rk-kaps/RKS-KEYBOARD/PCB/PCB.kicad_sch

## KiCad design PCB/PCB.kicad_sch (2026-03-29)

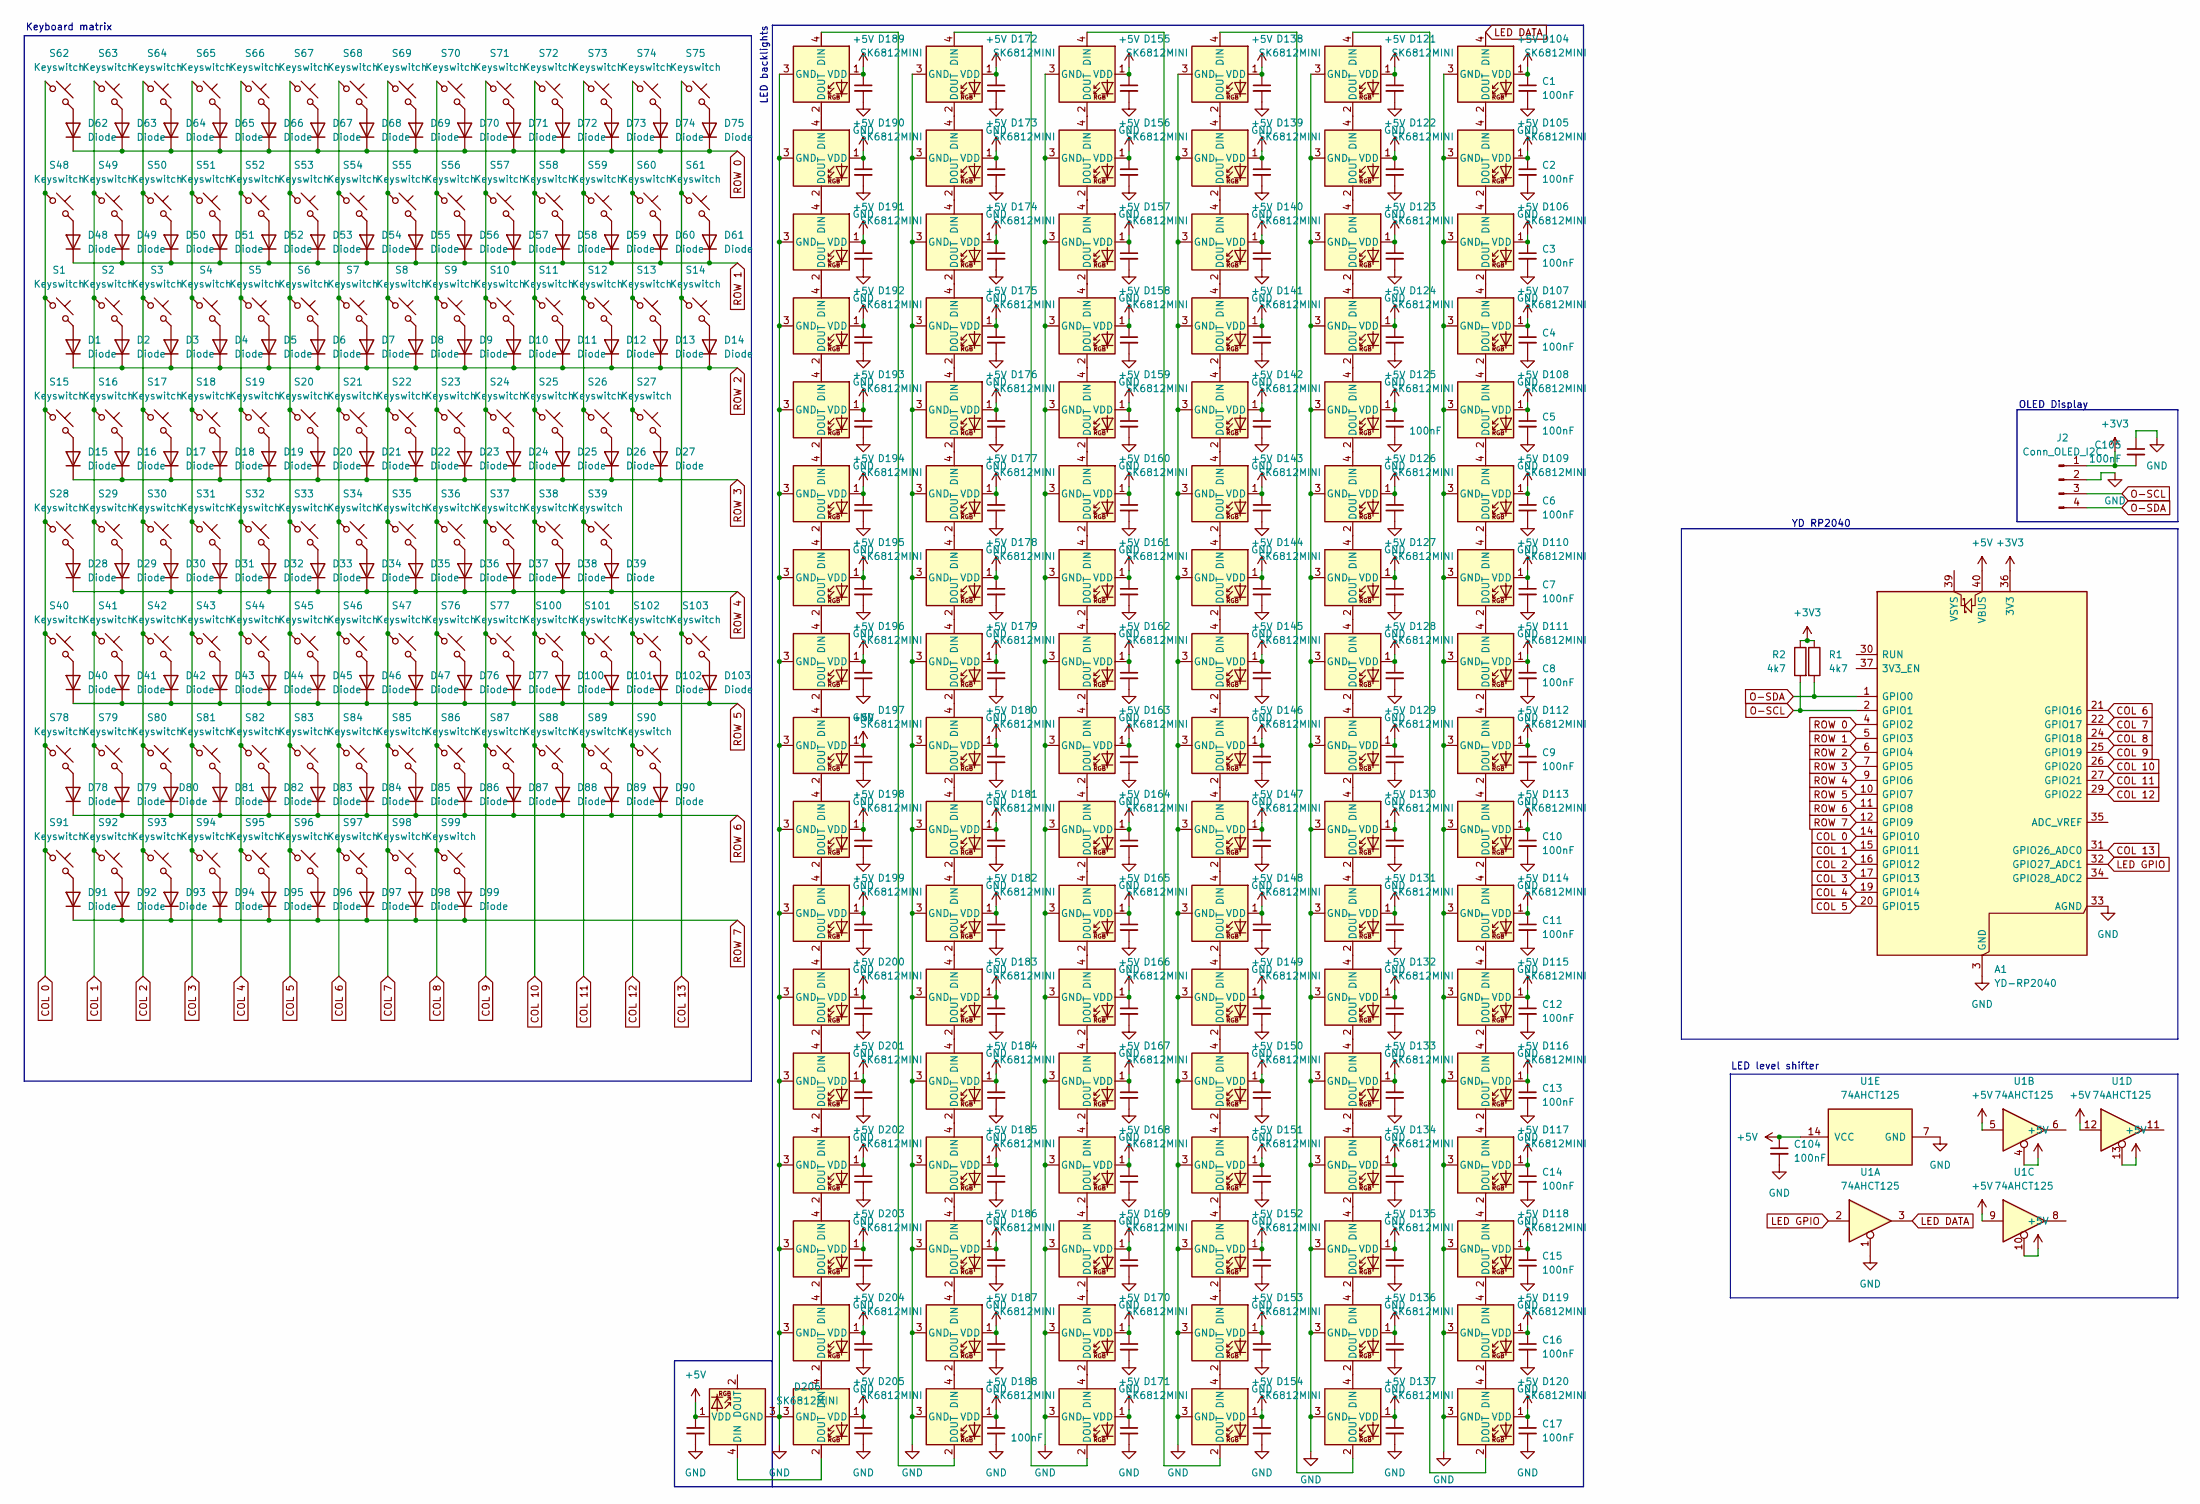
[picture p13: schematic PCB.kicad_sch]

Parts:
A1: YD-RP2040; RaspberryPi_Pico_SMD_HandSolder
C1, C2, C3, C4, C5, C6, C7, C8, C9, C10, C11, C12, C13, C14, C15, C16, C17, C18, C19, C20, C21, C22, C23, C24, C25, C26, C27, C28, C29, C30, C31, C32, C33, C34, C35, C36, C37, C38, C39, C40, C41, C42, C43, C44, C45, C46, C47, C48, C49, C50, C51, C52, C53, C54, C55, C56, C57, C58, C59, C60, C61, C62, C63, C64, C65, C66, C67, C68, C69, C70, C71, C72, C73, C74, C75, C76, C77, C78, C79, C80, C81, C82, C83, C84, C85, C86, C87, C88, C89, C90, C91, C92, C93, C94, C95, C96, C97, C98, C99, C100, C101, C102, C103, C104, C105: 100nF; C_0805_2012Metric_Pad1.18x1.45mm_HandSolder
D1, D2, D3, D4, D5, D6, D7, D8, D9, D10, D11, D12, D13, D14, D15, D16, D17, D18, D19, D20, D21, D22, D23, D24, D25, D26, D27, D28, D29, D30, D31, D32, D33, D34, D35, D36, D37, D38, D39, D40, D41, D42, D43, D44, D45, D46, D47, D48, D49, D50, D51, D52, D53, D54, D55, D56, D57, D58, D59, D60, D61, D62, D63, D64, D65, D66, D67, D68, D69, D70, D71, D72, D73, D74, D75, D76, D77, D78, D79, D80, D81, D82, D83, D84, D85, D86, D87, D88, D89, D90, D91, D92, D93, D94, D95, D96, D97, D98, D99, D100, D101, D102, D103: Diode; Diode_SOD-123
D104, D105, D106, D107, D108, D109, D110, D111, D112, D113, D114, D115, D116, D117, D118, D119, D120, D121, D122, D123, D124, D125, D126, D127, D128, D129, D130, D131, D132, D133, D134, D135, D136, D137, D138, D139, D140, D141, D142, D143, D144, D145, D146, D147, D148, D149, D150, D151, D152, D153, D154, D155, D156, D157, D158, D159, D160, D161, D162, D163, D164, D165, D166, D167, D168, D169, D170, D171, D172, D173, D174, D175, D176, D177, D178, D179, D180, D181, D182, D183, D184, D185, D186, D187, D188, D189, D190, D191, D192, D193, D194, D195, D196, D197, D198, D199, D200, D201, D202, D203, D204, D205, D206: SK6812MINI; LED_SK6812MINI
J2: Conn_OLED_I2C; PinHeader_1x04_P2.54mm_Vertical
R1, R2: 4k7; R_0805_2012Metric_Pad1.20x1.40mm_HandSolder
S1, S14: Keyswitch; Hotswap_MX_1.50u
S2, S3, S4, S5, S6, S7, S8, S9, S10, S11, S12, S13, S16, S17, S18, S19, S20, S21, S22, S23, S24, S25, S26, S29, S30, S31, S32, S33, S34, S35, S36, S37, S38, S44, S45, S46, S47, S48, S49, S50, S51, S52, S53, S54, S55, S56, S57, S58, S59, S60, S62, S63, S64, S65, S66, S67, S68, S69, S70, S71, S72, S73, S74, S75, S76, S77, S78, S79, S80, S81, S82, S83, S84, S85, S86, S87, S88, S89, S90, S91, S92, S95, S96, S97, S98, S99, S100, S101, S102, S103: Keyswitch; Hotswap_MX_1.00u
S15, S39: Keyswitch; Hotswap_MX_1.75u
S27, S28: Keyswitch; Hotswap_MX_2.25u
S40, S41, S42: Keyswitch; Hotswap_MX_1.25u
S43: Keyswitch; Hotswap_MX_6.25u
S61: Keyswitch; Hotswap_MX_2.00u
S93, S94: Keyswitch; Hotswap_MX_2.00u_90deg
U1: 74AHCT125; SOIC-14_3.9x8.7mm_P1.27mm

Connections:
+3V3: A1.36 (3V3), C105.2, J2.1, R1.1, R2.1
+5V: A1.40 (VBUS), C1.1, C2.1, C3.1, C4.1, C5.1, C6.1, C7.1, C8.1, C9.1, C10.1, C11.1, C12.1, C13.1, C14.1, C15.1, C16.1, C17.1, C18.1, C19.1, C20.1, C21.1, C22.1, C23.1, C24.1, C25.1, C26.1, C27.1, C28.1, C29.1, C30.1, C31.1, C32.1, C33.1, C34.1, C35.1, C36.1, C37.1, C38.1, C39.1, C40.1, C41.1, C42.1, C43.1, C44.1, C45.1, C46.1, C47.1, C48.1, C49.1, C50.1, C51.1, C52.1, C53.1, C54.1, C55.1, C56.1, C57.1, C58.1, C59.1, C60.1, C61.1, C62.1, C63.1, C64.1, C65.1, C66.1, C67.1, C68.1, C69.1, C70.1, C71.1, C72.1, C73.1, C74.1, C75.1, C76.1, C77.1, C78.1, C79.1, C80.1, C81.1, C82.1, C83.1, C84.1, C85.1, C86.1, C87.1, C88.1, C89.1, C90.1, C91.1, C92.1, C93.1, C94.1, C95.1, C96.1, C97.1, C98.1, C99.1, C100.1, C101.1, C102.1, C103.1, C104.1, D104.1 (VDD), D105.1 (VDD), D106.1 (VDD), D107.1 (VDD), D108.1 (VDD), D109.1 (VDD), D110.1 (VDD), D111.1 (VDD), D112.1 (VDD), D113.1 (VDD), D114.1 (VDD), D115.1 (VDD), D116.1 (VDD), D117.1 (VDD), D118.1 (VDD), D119.1 (VDD), D120.1 (VDD), D121.1 (VDD), D122.1 (VDD), D123.1 (VDD), D124.1 (VDD), D125.1 (VDD), D126.1 (VDD), D127.1 (VDD), D128.1 (VDD), D129.1 (VDD), D130.1 (VDD), D131.1 (VDD), D132.1 (VDD), D133.1 (VDD), D134.1 (VDD), D135.1 (VDD), D136.1 (VDD), D137.1 (VDD), D138.1 (VDD), D139.1 (VDD), D140.1 (VDD), D141.1 (VDD), D142.1 (VDD), D143.1 (VDD), D144.1 (VDD), D145.1 (VDD), D146.1 (VDD), D147.1 (VDD), D148.1 (VDD), D149.1 (VDD), D150.1 (VDD), D151.1 (VDD), D152.1 (VDD), D153.1 (VDD), D154.1 (VDD), D155.1 (VDD), D156.1 (VDD), D157.1 (VDD), D158.1 (VDD), D159.1 (VDD), D160.1 (VDD), D161.1 (VDD), D162.1 (VDD), D163.1 (VDD), D164.1 (VDD), D165.1 (VDD), D166.1 (VDD), D167.1 (VDD), D168.1 (VDD), D169.1 (VDD), D170.1 (VDD), D171.1 (VDD), D172.1 (VDD), D173.1 (VDD), D174.1 (VDD), D175.1 (VDD), D176.1 (VDD), D177.1 (VDD), D178.1 (VDD), D179.1 (VDD), D180.1 (VDD), D181.1 (VDD), D182.1 (VDD), D183.1 (VDD), D184.1 (VDD), D185.1 (VDD), D186.1 (VDD), D187.1 (VDD), D188.1 (VDD), D189.1 (VDD), D190.1 (VDD), D191.1 (VDD), D192.1 (VDD), D193.1 (VDD), D194.1 (VDD), D195.1 (VDD), D196.1 (VDD), D197.1 (VDD), D198.1 (VDD), D199.1 (VDD), D200.1 (VDD), D201.1 (VDD), D202.1 (VDD), D203.1 (VDD), D204.1 (VDD), D205.1 (VDD), D206.1 (VDD), U1.4, U1.5, U1.9, U1.10, U1.12, U1.13, U1.14 (VCC)
COL 0: A1.14 (GPIO10), S1.1, S15.1, S28.1, S40.1, S48.1, S62.1, S78.1, S91.1
COL 1: A1.15 (GPIO11), S2.1, S16.1, S29.1, S41.1, S49.1, S63.1, S79.1, S92.1
COL 2: A1.16 (GPIO12), S3.1, S17.1, S30.1, S42.1, S50.1, S64.1, S80.1, S93.1
COL 3: A1.17 (GPIO13), S4.1, S18.1, S31.1, S43.1, S51.1, S65.1, S81.1, S94.1
COL 4: A1.19 (GPIO14), S5.1, S19.1, S32.1, S44.1, S52.1, S66.1, S82.1, S95.1
COL 5: A1.20 (GPIO15), S6.1, S20.1, S33.1, S45.1, S53.1, S67.1, S83.1, S96.1
COL 6: A1.21 (GPIO16), S7.1, S21.1, S34.1, S46.1, S54.1, S68.1, S84.1, S97.1
COL 7: A1.22 (GPIO17), S8.1, S22.1, S35.1, S47.1, S55.1, S69.1, S85.1, S98.1
COL 8: A1.24 (GPIO18), S9.1, S23.1, S36.1, S56.1, S70.1, S76.1, S86.1, S99.1
COL 9: A1.25 (GPIO19), S10.1, S24.1, S37.1, S57.1, S71.1, S77.1, S87.1
COL 10: A1.26 (GPIO20), S11.1, S25.1, S38.1, S58.1, S72.1, S88.1, S100.1
COL 11: A1.27 (GPIO21), S12.1, S26.1, S39.1, S59.1, S73.1, S89.1, S101.1
COL 12: A1.29 (GPIO22), S13.1, S27.1, S60.1, S74.1, S90.1, S102.1
COL 13: A1.31 (GPIO26_ADC0), S14.1, S61.1, S75.1, S103.1
GND: A1.3 (GND), A1.8 (GND), A1.13 (GND), A1.18 (GND), A1.23 (GND), A1.28 (GND), A1.33 (AGND), A1.38 (GND), C1.2, C2.2, C3.2, C4.2, C5.2, C6.2, C7.2, C8.2, C9.2, C10.2, C11.2, C12.2, C13.2, C14.2, C15.2, C16.2, C17.2, C18.2, C19.2, C20.2, C21.2, C22.2, C23.2, C24.2, C25.2, C26.2, C27.2, C28.2, C29.2, C30.2, C31.2, C32.2, C33.2, C34.2, C35.2, C36.2, C37.2, C38.2, C39.2, C40.2, C41.2, C42.2, C43.2, C44.2, C45.2, C46.2, C47.2, C48.2, C49.2, C50.2, C51.2, C52.2, C53.2, C54.2, C55.2, C56.2, C57.2, C58.2, C59.2, C60.2, C61.2, C62.2, C63.2, C64.2, C65.2, C66.2, C67.2, C68.2, C69.2, C70.2, C71.2, C72.2, C73.2, C74.2, C75.2, C76.2, C77.2, C78.2, C79.2, C80.2, C81.2, C82.2, C83.2, C84.2, C85.2, C86.2, C87.2, C88.2, C89.2, C90.2, C91.2, C92.2, C93.2, C94.2, C95.2, C96.2, C97.2, C98.2, C99.2, C100.2, C101.2, C102.2, C103.2, C104.2, C105.1, D104.3 (GND), D105.3 (GND), D106.3 (GND), D107.3 (GND), D108.3 (GND), D109.3 (GND), D110.3 (GND), D111.3 (GND), D112.3 (GND), D113.3 (GND), D114.3 (GND), D115.3 (GND), D116.3 (GND), D117.3 (GND), D118.3 (GND), D119.3 (GND), D120.3 (GND), D121.3 (GND), D122.3 (GND), D123.3 (GND), D124.3 (GND), D125.3 (GND), D126.3 (GND), D127.3 (GND), D128.3 (GND), D129.3 (GND), D130.3 (GND), D131.3 (GND), D132.3 (GND), D133.3 (GND), D134.3 (GND), D135.3 (GND), D136.3 (GND), D137.3 (GND), D138.3 (GND), D139.3 (GND), D140.3 (GND), D141.3 (GND), D142.3 (GND), D143.3 (GND), D144.3 (GND), D145.3 (GND), D146.3 (GND), D147.3 (GND), D148.3 (GND), D149.3 (GND), D150.3 (GND), D151.3 (GND), D152.3 (GND), D153.3 (GND), D154.3 (GND), D155.3 (GND), D156.3 (GND), D157.3 (GND), D158.3 (GND), D159.3 (GND), D160.3 (GND), D161.3 (GND), D162.3 (GND), D163.3 (GND), D164.3 (GND), D165.3 (GND), D166.3 (GND), D167.3 (GND), D168.3 (GND), D169.3 (GND), D170.3 (GND), D171.3 (GND), D172.3 (GND), D173.3 (GND), D174.3 (GND), D175.3 (GND), D176.3 (GND), D177.3 (GND), D178.3 (GND), D179.3 (GND), D180.3 (GND), D181.3 (GND), D182.3 (GND), D183.3 (GND), D184.3 (GND), D185.3 (GND), D186.3 (GND), D187.3 (GND), D188.3 (GND), D189.3 (GND), D190.3 (GND), D191.3 (GND), D192.3 (GND), D193.3 (GND), D194.3 (GND), D195.3 (GND), D196.3 (GND), D197.3 (GND), D198.3 (GND), D199.3 (GND), D200.3 (GND), D201.3 (GND), D202.3 (GND), D203.3 (GND), D204.3 (GND), D205.3 (GND), D206.3 (GND), J2.2, U1.1, U1.7 (GND)
LED DATA: D104.4 (DIN), U1.3
LED GPIO: A1.32 (GPIO27_ADC1), U1.2
unnamed: D1.2 (A), S1.2
unnamed: D2.2 (A), S2.2
unnamed: D3.2 (A), S3.2
unnamed: D4.2 (A), S4.2
unnamed: D5.2 (A), S5.2
unnamed: D6.2 (A), S6.2
unnamed: D7.2 (A), S7.2
unnamed: D8.2 (A), S8.2
unnamed: D9.2 (A), S9.2
unnamed: D10.2 (A), S10.2
unnamed: D11.2 (A), S11.2
unnamed: D12.2 (A), S12.2
unnamed: D13.2 (A), S13.2
unnamed: D14.2 (A), S14.2
unnamed: D15.2 (A), S15.2
unnamed: D16.2 (A), S16.2
unnamed: D17.2 (A), S17.2
unnamed: D18.2 (A), S18.2
unnamed: D19.2 (A), S19.2
unnamed: D20.2 (A), S20.2
unnamed: D21.2 (A), S21.2
unnamed: D22.2 (A), S22.2
unnamed: D23.2 (A), S23.2
unnamed: D24.2 (A), S24.2
unnamed: D25.2 (A), S25.2
unnamed: D26.2 (A), S26.2
unnamed: D27.2 (A), S27.2
unnamed: D28.2 (A), S28.2
unnamed: D29.2 (A), S29.2
unnamed: D30.2 (A), S30.2
unnamed: D31.2 (A), S31.2
unnamed: D32.2 (A), S32.2
unnamed: D33.2 (A), S33.2
unnamed: D34.2 (A), S34.2
unnamed: D35.2 (A), S35.2
unnamed: D36.2 (A), S36.2
unnamed: D37.2 (A), S37.2
unnamed: D38.2 (A), S38.2
unnamed: D39.2 (A), S39.2
unnamed: D40.2 (A), S40.2
unnamed: D41.2 (A), S41.2
unnamed: D42.2 (A), S42.2
unnamed: D43.2 (A), S43.2
unnamed: D44.2 (A), S44.2
unnamed: D45.2 (A), S45.2
unnamed: D46.2 (A), S46.2
unnamed: D47.2 (A), S47.2
unnamed: D48.2 (A), S48.2
unnamed: D49.2 (A), S49.2
unnamed: D50.2 (A), S50.2
unnamed: D51.2 (A), S51.2
unnamed: D52.2 (A), S52.2
unnamed: D53.2 (A), S53.2
unnamed: D54.2 (A), S54.2
unnamed: D55.2 (A), S55.2
unnamed: D56.2 (A), S56.2
unnamed: D57.2 (A), S57.2
unnamed: D58.2 (A), S58.2
unnamed: D59.2 (A), S59.2
unnamed: D60.2 (A), S60.2
unnamed: D61.2 (A), S61.2
unnamed: D62.2 (A), S62.2
unnamed: D63.2 (A), S63.2
unnamed: D64.2 (A), S64.2
unnamed: D65.2 (A), S65.2
unnamed: D66.2 (A), S66.2
unnamed: D67.2 (A), S67.2
unnamed: D68.2 (A), S68.2
unnamed: D69.2 (A), S69.2
unnamed: D70.2 (A), S70.2
unnamed: D71.2 (A), S71.2
unnamed: D72.2 (A), S72.2
unnamed: D73.2 (A), S73.2
unnamed: D74.2 (A), S74.2
unnamed: D75.2 (A), S75.2
unnamed: D76.2 (A), S76.2
unnamed: D77.2 (A), S77.2
unnamed: D78.2 (A), S78.2
unnamed: D79.2 (A), S79.2
unnamed: D80.2 (A), S80.2
unnamed: D81.2 (A), S81.2
unnamed: D82.2 (A), S82.2
unnamed: D83.2 (A), S83.2
unnamed: D84.2 (A), S84.2
unnamed: D85.2 (A), S85.2
unnamed: D86.2 (A), S86.2
unnamed: D87.2 (A), S87.2
unnamed: D88.2 (A), S88.2
unnamed: D89.2 (A), S89.2
unnamed: D90.2 (A), S90.2
unnamed: D91.2 (A), S91.2
unnamed: D92.2 (A), S92.2
unnamed: D93.2 (A), S93.2
unnamed: D94.2 (A), S94.2
unnamed: D95.2 (A), S95.2
unnamed: D96.2 (A), S96.2
unnamed: D97.2 (A), S97.2
unnamed: D98.2 (A), S98.2
unnamed: D99.2 (A), S99.2
unnamed: D100.2 (A), S100.2
unnamed: D101.2 (A), S101.2
unnamed: D102.2 (A), S102.2
unnamed: D103.2 (A), S103.2
unnamed: D104.2 (DOUT), D105.4 (DIN)
unnamed: D105.2 (DOUT), D106.4 (DIN)
unnamed: D106.2 (DOUT), D107.4 (DIN)
unnamed: D107.2 (DOUT), D108.4 (DIN)
unnamed: D108.2 (DOUT), D109.4 (DIN)
unnamed: D109.2 (DOUT), D110.4 (DIN)
unnamed: D110.2 (DOUT), D111.4 (DIN)
unnamed: D111.2 (DOUT), D112.4 (DIN)
unnamed: D112.2 (DOUT), D113.4 (DIN)
unnamed: D113.2 (DOUT), D114.4 (DIN)
unnamed: D114.2 (DOUT), D115.4 (DIN)
unnamed: D115.2 (DOUT), D116.4 (DIN)
unnamed: D116.2 (DOUT), D117.4 (DIN)
unnamed: D117.2 (DOUT), D118.4 (DIN)
unnamed: D118.2 (DOUT), D119.4 (DIN)
unnamed: D119.2 (DOUT), D120.4 (DIN)
unnamed: D120.2 (DOUT), D121.4 (DIN)
unnamed: D121.2 (DOUT), D122.4 (DIN)
unnamed: D122.2 (DOUT), D123.4 (DIN)
unnamed: D123.2 (DOUT), D124.4 (DIN)
unnamed: D124.2 (DOUT), D125.4 (DIN)
unnamed: D125.2 (DOUT), D126.4 (DIN)
unnamed: D126.2 (DOUT), D127.4 (DIN)
unnamed: D127.2 (DOUT), D128.4 (DIN)
unnamed: D128.2 (DOUT), D129.4 (DIN)
unnamed: D129.2 (DOUT), D130.4 (DIN)
unnamed: D130.2 (DOUT), D131.4 (DIN)
unnamed: D131.2 (DOUT), D132.4 (DIN)
unnamed: D132.2 (DOUT), D133.4 (DIN)
unnamed: D133.2 (DOUT), D134.4 (DIN)
unnamed: D134.2 (DOUT), D135.4 (DIN)
unnamed: D135.2 (DOUT), D136.4 (DIN)
unnamed: D136.2 (DOUT), D137.4 (DIN)
unnamed: D137.2 (DOUT), D138.4 (DIN)
unnamed: D138.2 (DOUT), D139.4 (DIN)
unnamed: D139.2 (DOUT), D140.4 (DIN)
unnamed: D140.2 (DOUT), D141.4 (DIN)
unnamed: D141.2 (DOUT), D142.4 (DIN)
unnamed: D142.2 (DOUT), D143.4 (DIN)
unnamed: D143.2 (DOUT), D144.4 (DIN)
unnamed: D144.2 (DOUT), D145.4 (DIN)
unnamed: D145.2 (DOUT), D146.4 (DIN)
unnamed: D146.2 (DOUT), D147.4 (DIN)
unnamed: D147.2 (DOUT), D148.4 (DIN)
unnamed: D148.2 (DOUT), D149.4 (DIN)
unnamed: D149.2 (DOUT), D150.4 (DIN)
unnamed: D150.2 (DOUT), D151.4 (DIN)
unnamed: D151.2 (DOUT), D152.4 (DIN)
unnamed: D152.2 (DOUT), D153.4 (DIN)
unnamed: D153.2 (DOUT), D154.4 (DIN)
unnamed: D154.2 (DOUT), D155.4 (DIN)
unnamed: D155.2 (DOUT), D156.4 (DIN)
unnamed: D156.2 (DOUT), D157.4 (DIN)
unnamed: D157.2 (DOUT), D158.4 (DIN)
unnamed: D158.2 (DOUT), D159.4 (DIN)
unnamed: D159.2 (DOUT), D160.4 (DIN)
unnamed: D160.2 (DOUT), D161.4 (DIN)
unnamed: D161.2 (DOUT), D162.4 (DIN)
unnamed: D162.2 (DOUT), D163.4 (DIN)
unnamed: D163.2 (DOUT), D164.4 (DIN)
unnamed: D164.2 (DOUT), D165.4 (DIN)
unnamed: D165.2 (DOUT), D166.4 (DIN)
unnamed: D166.2 (DOUT), D167.4 (DIN)
unnamed: D167.2 (DOUT), D168.4 (DIN)
unnamed: D168.2 (DOUT), D169.4 (DIN)
unnamed: D169.2 (DOUT), D170.4 (DIN)
unnamed: D170.2 (DOUT), D171.4 (DIN)
unnamed: D171.2 (DOUT), D172.4 (DIN)
unnamed: D172.2 (DOUT), D173.4 (DIN)
unnamed: D173.2 (DOUT), D174.4 (DIN)
unnamed: D174.2 (DOUT), D175.4 (DIN)
unnamed: D175.2 (DOUT), D176.4 (DIN)
unnamed: D176.2 (DOUT), D177.4 (DIN)
unnamed: D177.2 (DOUT), D178.4 (DIN)
unnamed: D178.2 (DOUT), D179.4 (DIN)
unnamed: D179.2 (DOUT), D180.4 (DIN)
unnamed: D180.2 (DOUT), D181.4 (DIN)
unnamed: D181.2 (DOUT), D182.4 (DIN)
unnamed: D182.2 (DOUT), D183.4 (DIN)
unnamed: D183.2 (DOUT), D184.4 (DIN)
unnamed: D184.2 (DOUT), D185.4 (DIN)
unnamed: D185.2 (DOUT), D186.4 (DIN)
unnamed: D186.2 (DOUT), D187.4 (DIN)
unnamed: D187.2 (DOUT), D188.4 (DIN)
unnamed: D188.2 (DOUT), D189.4 (DIN)
unnamed: D189.2 (DOUT), D190.4 (DIN)
unnamed: D190.2 (DOUT), D191.4 (DIN)
unnamed: D191.2 (DOUT), D192.4 (DIN)
unnamed: D192.2 (DOUT), D193.4 (DIN)
unnamed: D193.2 (DOUT), D194.4 (DIN)
unnamed: D194.2 (DOUT), D195.4 (DIN)
unnamed: D195.2 (DOUT), D196.4 (DIN)
unnamed: D196.2 (DOUT), D197.4 (DIN)
unnamed: D197.2 (DOUT), D198.4 (DIN)
unnamed: D198.2 (DOUT), D199.4 (DIN)
unnamed: D199.2 (DOUT), D200.4 (DIN)
unnamed: D200.2 (DOUT), D201.4 (DIN)
unnamed: D201.2 (DOUT), D202.4 (DIN)
unnamed: D202.2 (DOUT), D203.4 (DIN)
unnamed: D203.2 (DOUT), D204.4 (DIN)
unnamed: D204.2 (DOUT), D205.4 (DIN)
unnamed: D205.2 (DOUT), D206.4 (DIN)
O-SCL: A1.2 (GPIO1), J2.3, R2.2
O-SDA: A1.1 (GPIO0), J2.4, R1.2
ROW 0: A1.4 (GPIO2), D62.1 (K), D63.1 (K), D64.1 (K), D65.1 (K), D66.1 (K), D67.1 (K), D68.1 (K), D69.1 (K), D70.1 (K), D71.1 (K), D72.1 (K), D73.1 (K), D74.1 (K), D75.1 (K)
ROW 1: A1.5 (GPIO3), D48.1 (K), D49.1 (K), D50.1 (K), D51.1 (K), D52.1 (K), D53.1 (K), D54.1 (K), D55.1 (K), D56.1 (K), D57.1 (K), D58.1 (K), D59.1 (K), D60.1 (K), D61.1 (K)
ROW 2: A1.6 (GPIO4), D1.1 (K), D2.1 (K), D3.1 (K), D4.1 (K), D5.1 (K), D6.1 (K), D7.1 (K), D8.1 (K), D9.1 (K), D10.1 (K), D11.1 (K), D12.1 (K), D13.1 (K), D14.1 (K)
ROW 3: A1.7 (GPIO5), D15.1 (K), D16.1 (K), D17.1 (K), D18.1 (K), D19.1 (K), D20.1 (K), D21.1 (K), D22.1 (K), D23.1 (K), D24.1 (K), D25.1 (K), D26.1 (K), D27.1 (K)
ROW 4: A1.9 (GPIO6), D28.1 (K), D29.1 (K), D30.1 (K), D31.1 (K), D32.1 (K), D33.1 (K), D34.1 (K), D35.1 (K), D36.1 (K), D37.1 (K), D38.1 (K), D39.1 (K)
ROW 5: A1.10 (GPIO7), D40.1 (K), D41.1 (K), D42.1 (K), D43.1 (K), D44.1 (K), D45.1 (K), D46.1 (K), D47.1 (K), D76.1 (K), D77.1 (K), D100.1 (K), D101.1 (K), D102.1 (K), D103.1 (K)
ROW 6: A1.11 (GPIO8), D78.1 (K), D79.1 (K), D80.1 (K), D81.1 (K), D82.1 (K), D83.1 (K), D84.1 (K), D85.1 (K), D86.1 (K), D87.1 (K), D88.1 (K), D89.1 (K), D90.1 (K)
ROW 7: A1.12 (GPIO9), D91.1 (K), D92.1 (K), D93.1 (K), D94.1 (K), D95.1 (K), D96.1 (K), D97.1 (K), D98.1 (K), D99.1 (K)

Notes on the sheet:
LED backlights
Keyboard matrix
OLED Display
YD RP2040
LED level shifter
